Gphoebus/peson/cao/demi_poigne1.SLDPRT

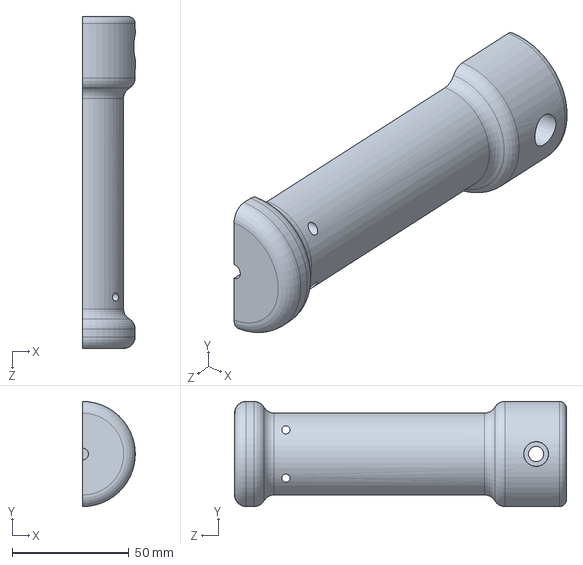
[picture p21: CAD file, 2026-04-23]
cao/demi_poigne1.SLDPRT
22.5 x 45.0 x 142.0 mm
