Gphoebus/peson/cao/GX-16 Connector 4 Pins.stp

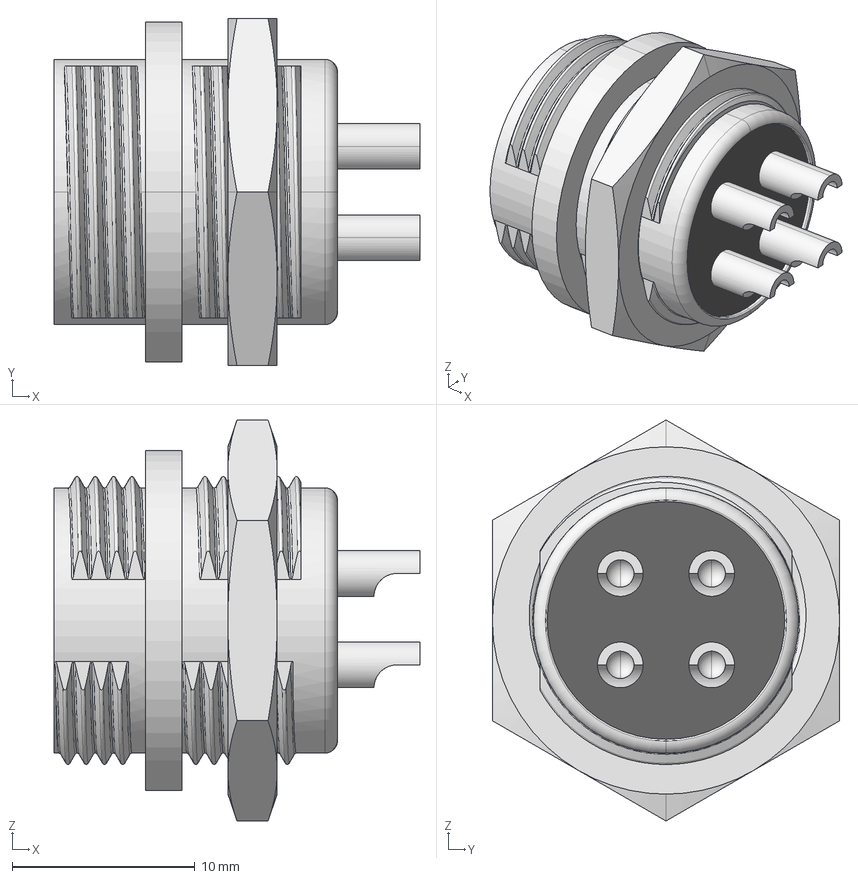
[picture p22: CAD file, 2026-04-23]
cao/GX-16 Connector 4 Pins.stp
20.0 x 19.0 x 21.9 mm
Nut
Isolator
Pins
